professor-jonny/Xbox-AVIP-mod/pictures/12122015188.jpg

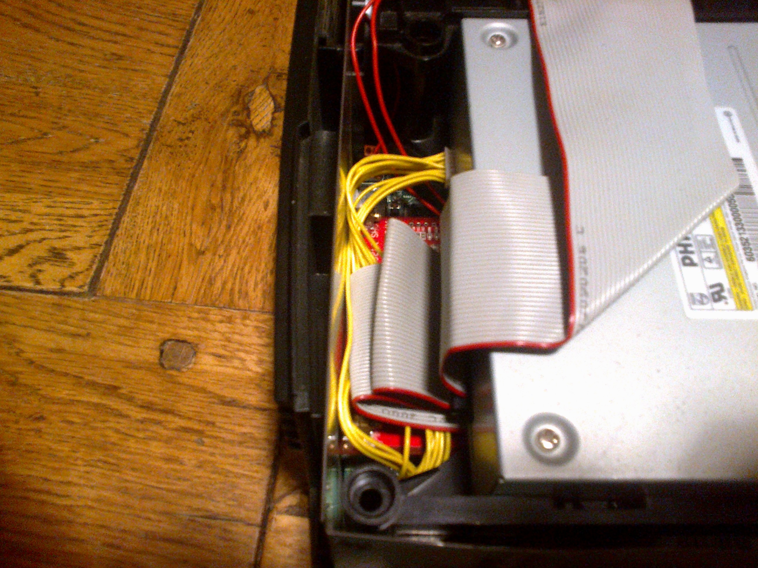
pictures/12122015188.jpg
