professor-jonny/Xbox-AVIP-mod/pictures/AVIP V2 fitted.jpg

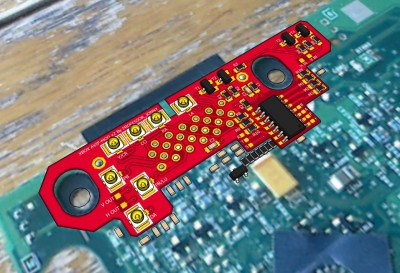
pictures/AVIP V2 fitted.jpg
