professor-jonny/Xbox-AVIP-mod/pictures/blank pcb model.jpg

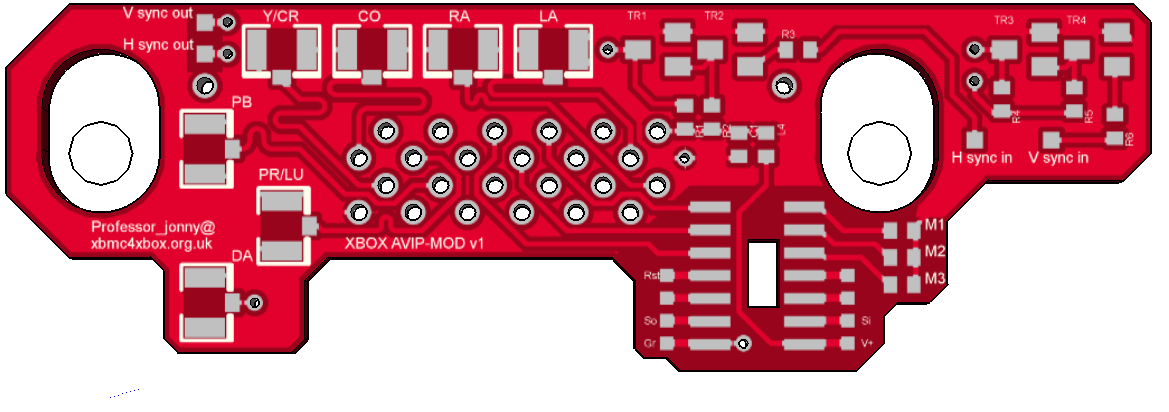
pictures/blank pcb model.jpg
