professor-jonny/Xbox-AVIP-mod/pictures/blank.JPG

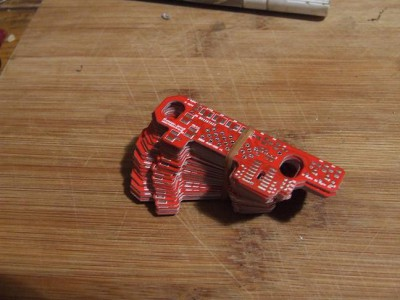
pictures/blank.JPG
