professor-jonny/Xbox-AVIP-mod/pictures/hdmi top u.fl.jpg

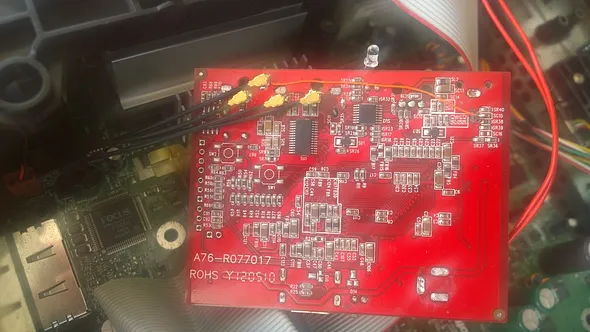
pictures/hdmi top u.fl.jpg
