professor-jonny/Xbox-AVIP-mod/pictures/motherboard fitted.jpg

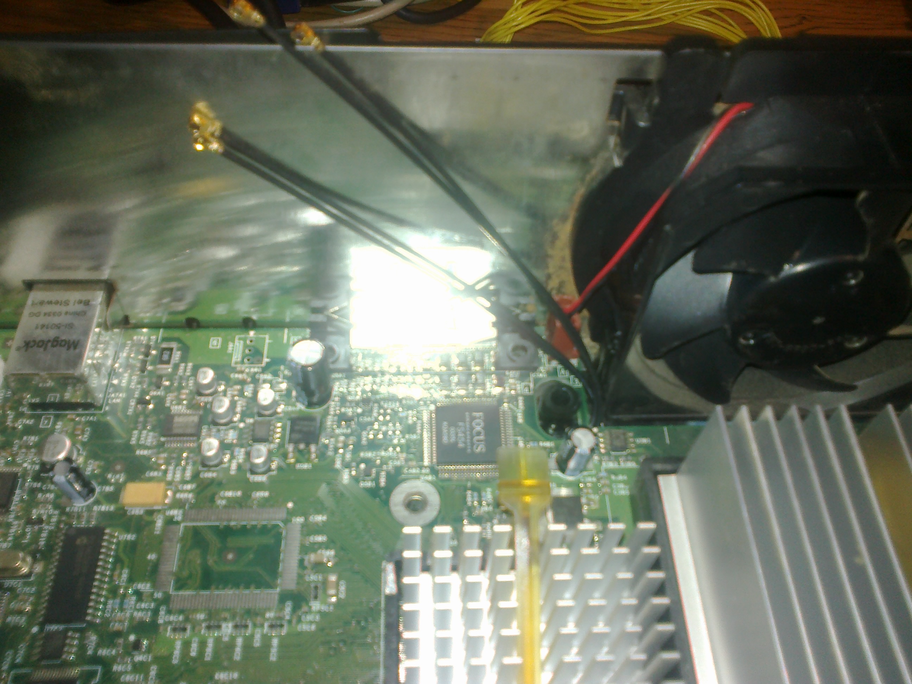
pictures/motherboard fitted.jpg
