professor-jonny/Xbox-AVIP-mod/pictures/populated bottom model.jpg

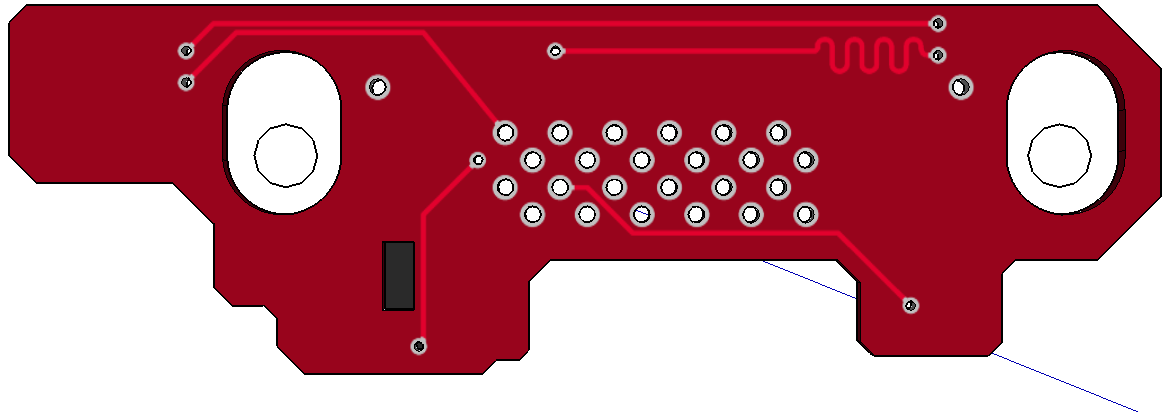
pictures/populated bottom model.jpg
