professor-jonny/Xbox-AVIP-mod/pictures/sound board.jpg

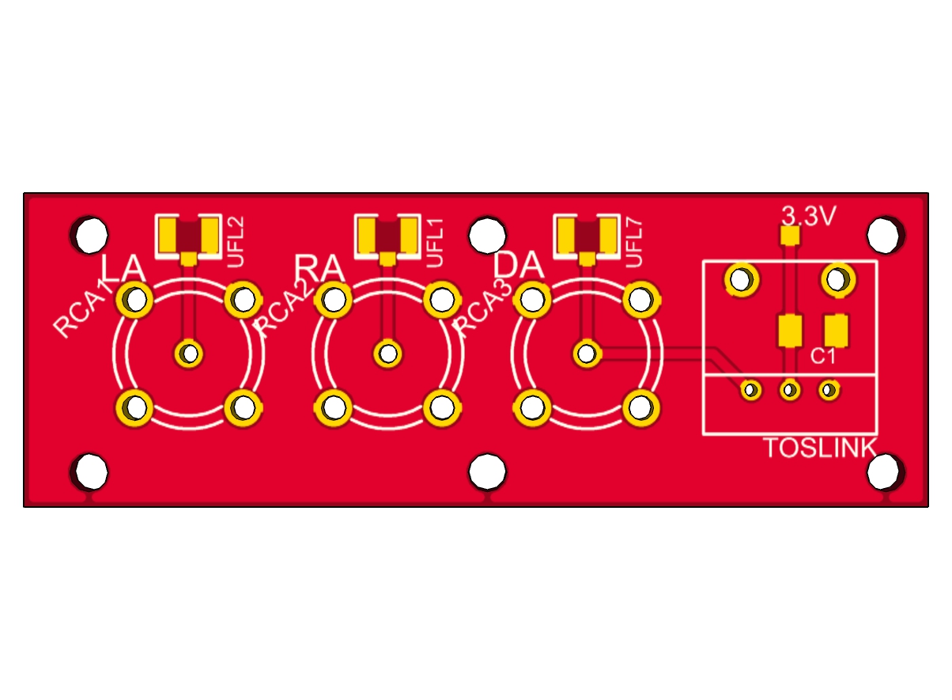
pictures/sound board.jpg
