professor-jonny/Xbox-AVIP-mod/pictures/v1 with ufl plugs fitted.JPG

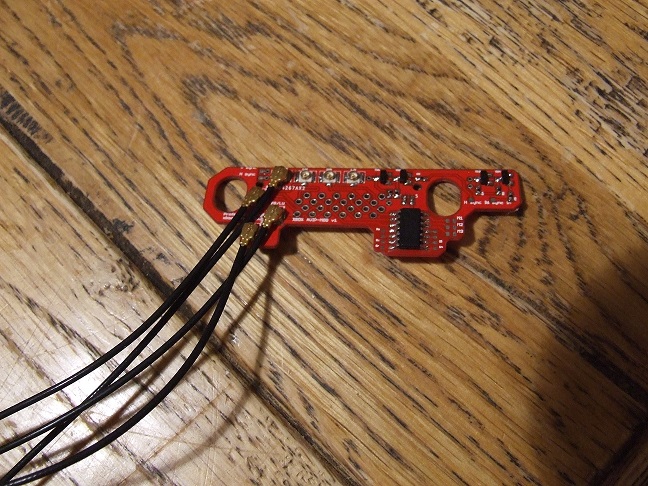
pictures/v1 with ufl plugs fitted.JPG
