professor-jonny/Xbox-AVIP-mod/pictures/vga board.jpg

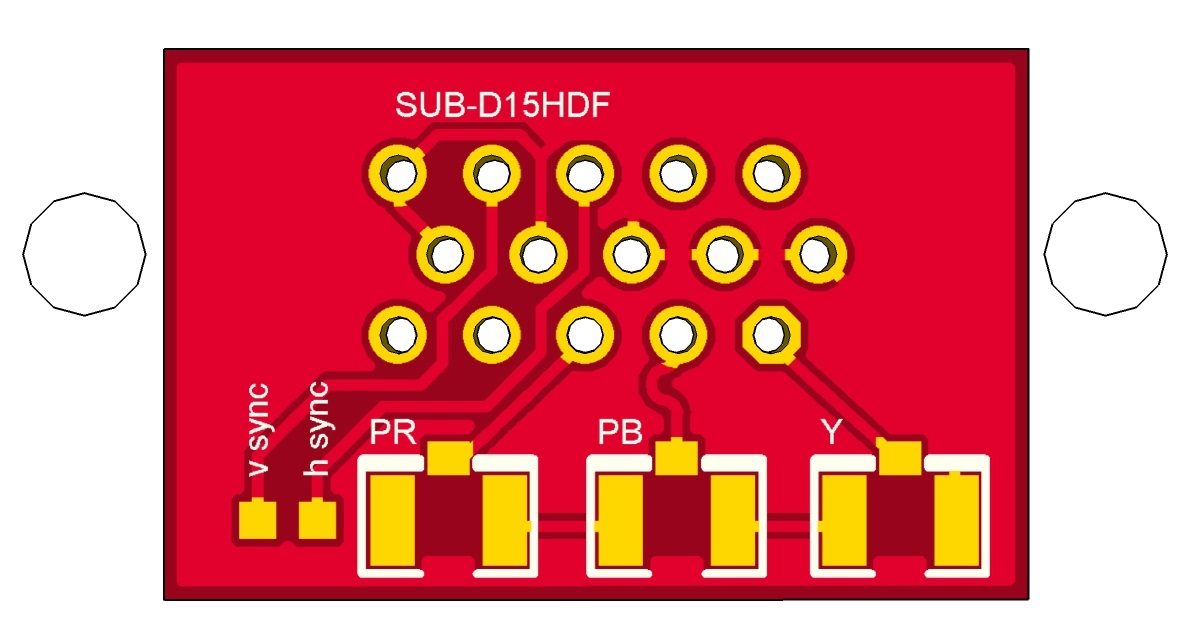
pictures/vga board.jpg
