professor-jonny/Xbox-AVIP-mod/pictures/vga model plug.jpg

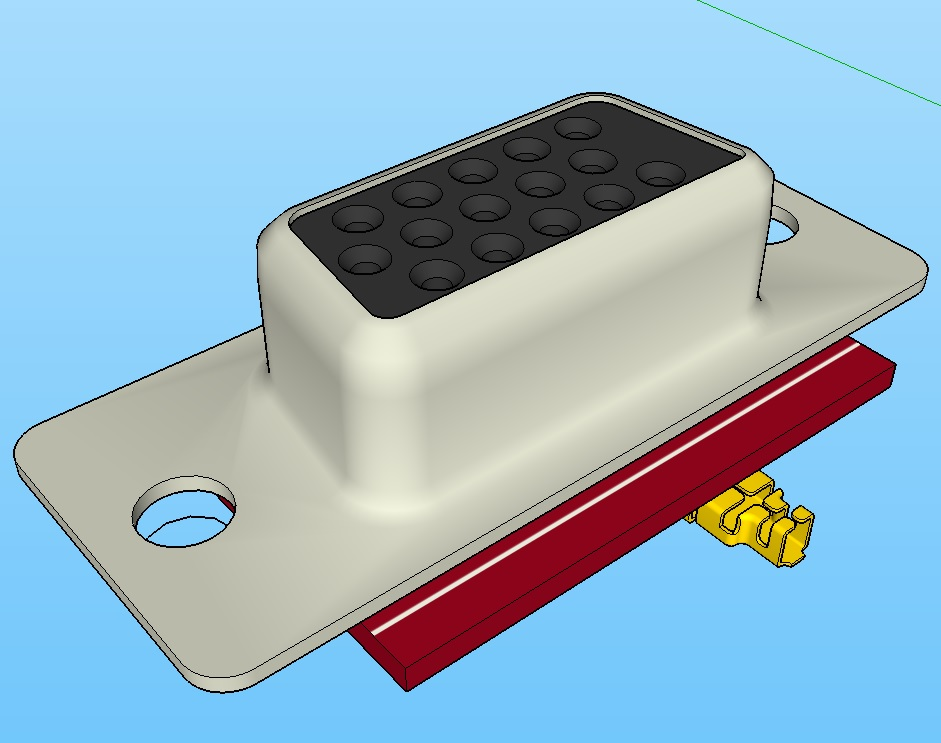
pictures/vga model plug.jpg
