professor-jonny/Xbox-AVIP-mod/pictures/Xbox v1.6 motherboard.jpg

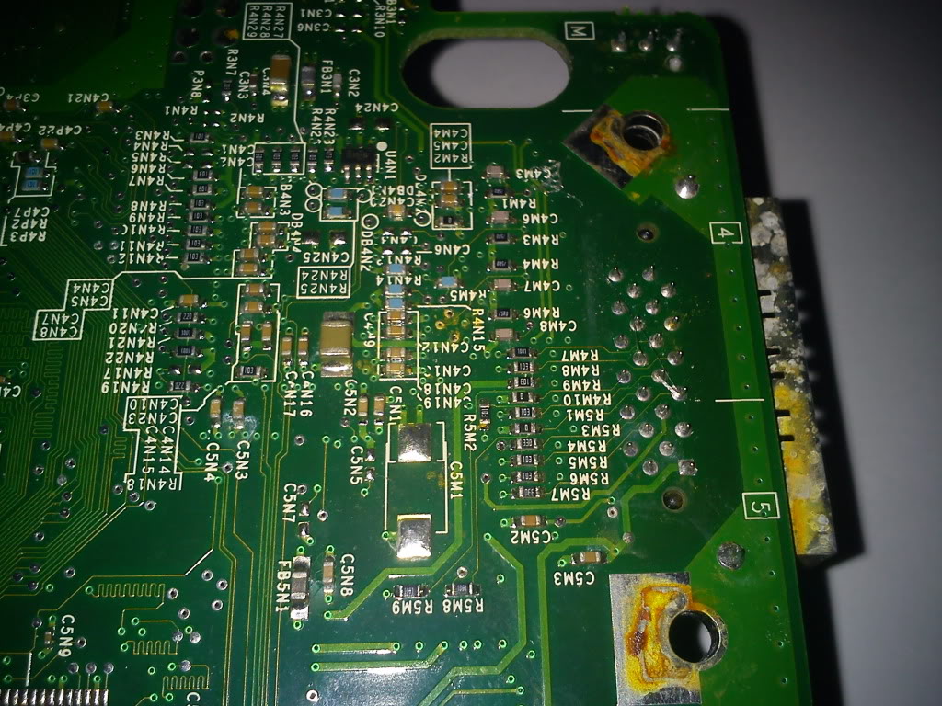
pictures/Xbox v1.6 motherboard.jpg
