professor-jonny/Xbox-AVIP-mod/pictures/component location.jpg

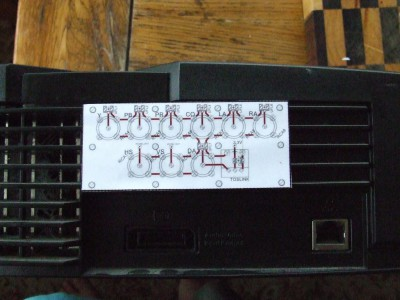
pictures/component location.jpg
