professor-jonny/Xbox-AVIP-mod/pictures/avip printed fitting.jpg

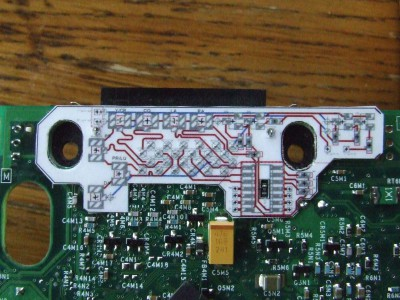
pictures/avip printed fitting.jpg
