professor-jonny/Xbox-AVIP-mod/pictures/vinyl printout.jpg

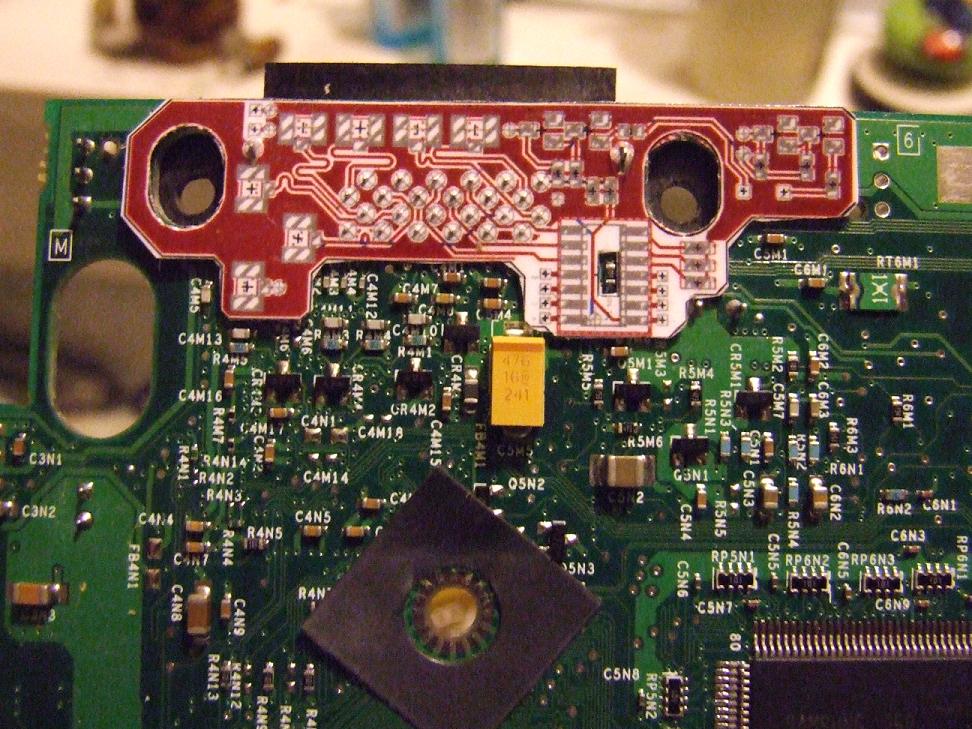
pictures/vinyl printout.jpg
